Tachy/Roboter/unkrautroboter_bilderkennung/src/status_bus.py

"""
Thread-safe status message bus to surface status texts to the web UI.
"""

import threading
import time
from typing import Optional, Dict, Any

_lock = threading.Lock()
_message: Optional[str] = None
_ts: float = 0.0
_arduino_status: Optional[Dict[str, Any]] = None
_arduino_ts: float = 0.0


def set_message(text: Optional[str]) -> None:
    global _message, _ts
    with _lock:
        _message = (text or "").strip() if text is not None else None
        _ts = time.time()


def get_message() -> Optional[str]:
    with _lock:
        return _message


def get_message_info():
    with _lock:
        return {"message": _message, "ts": _ts}


def set_arduino_status(status: Optional[Dict[str, Any]]) -> None:
    """Speichert den vom Arduino empfangenen STATUS-JSON."""
    global _arduino_status, _arduino_ts
    with _lock:
        _arduino_status = status
        _arduino_ts = time.time()


def get_arduino_status() -> Optional[Dict[str, Any]]:
    """Gibt den aktuellen Arduino-Status zurück."""
    with _lock:
        return _arduino_status
